psampsonee/elephant/hardware/LTSpice/buck-converter/tests/_archive/Sept 2026 Buck Converter Verification/notes/Curves/Energizer L92 - Internal Resistance Profile - X 0-1600 mAh - Y 0-0.8 Ohms.png.traj.ods

 | Pixels | Units
X | 272 | 400
Y | 174 | 0.2
Origin | 23
 | 704
Point | X-Pix | Y-Pix | mAh Used | Ohms
A | 23 | 424 | 0 | 0.11
 | 29 | 460 | 10 | 0.09
 | 50 | 484 | 43 | 0.08
 | 92 | 501 | 111 | 0.08
 | 150 | 511 | 204 | 0.07
 | 223 | 517 | 321 | 0.07
 | 297 | 521 | 440 | 0.07
 | 352 | 522 | 529 | 0.07
 | 570 | 537 | 879 | 0.06
 | 720 | 530 | 1120 | 0.07
 | 786 | 521 | 1226 | 0.07
 | 805 | 516 | 1256 | 0.07
 | 818 | 511 | 1277 | 0.07
 | 830 | 504 | 1296 | 0.08
 | 839 | 496 | 1311 | 0.08
 | 846 | 485 | 1322 | 0.08
 | 853 | 470 | 1333 | 0.09
 | 861 | 440 | 1346 | 0.10
 | 870 | 371 | 1361 | 0.13
 | 881 | 203 | 1378 | 0.19
 | 893 | 20 | 1398 | 0.26
