psampsonee/elephant/experiments/audio-test/LTSpice/dumb amplifier.asc

C1: cap; 10µ
C2: cap; {COUT}
C3: cap; 100n
D1: diode
D2: diode
Q1: npn
Q2: pnp
R1: res; 10k
R2: res; 10k
R3: res; 100
R4: res; {RBIAS}
R5: res; {RBIAS}
R6: res; {RLOAD}
R7: res; 4.7
R8: res; 4.7
Rf: res; 470k
Rin: res; 100k
U1: AD8542
V1: voltage; SINE({SIGOFF} {SIGAMP} {SIGF} 0); AC {SIGAMP} 0; Rser=10
V2: voltage; {VPOW}
Named nets: 0, VPow, VSig, VRef, VOut, Vout_OP, VB_Q1, VE_Q1, VB_Q2
.param VPOW=5
.param SIGMAXDC=3.3
.param SIGAMP=0.1
.param SIGOFF=SIGMAXDC/2
.param SIGF=50
 
.param RBIAS=1k
.param COUT=470u
.param RLOAD=7.3
.tran 0 1s 0
