psampsonee/elephant/hardware/LTSpice/buck-converter/Baseline/buck-test.asc

B1: bi; I={LOAD_I(V(V_BUCK_OUT),time)}
BATT1: L92; MAH_INIT={L92_MAH_INIT} L_SER=20n
BATT2: L92; MAH_INIT={L92_MAH_INIT} L_SER=20n
BATT3: L92; MAH_INIT={L92_MAH_INIT} L_SER=20n
BATT4: L92; MAH_INIT={L92_MAH_INIT} L_SER=20n
C1: cap; {C_1U}; V={C_1U_VOLTAGE_RATING} Rser={ESR_C_1U}
C2: cap; {C_TRSS}
C3: cap; {C_1U}; V={C_1U_VOLTAGE_RATING} Rser={ESR_C_1U}
C4: cap; {C_1U}; V={C_1U_VOLTAGE_RATING} Rser={ESR_C_1U}
C5: cap; {C_1U}; V={C_1U_VOLTAGE_RATING} Rser={ESR_C_1U}
C6: cap; {C_VIN_DISTAL}
C7: cap; {C_OUT}; IC={V_COUT_INIT}
C8: cap; {C_BIAS}
L1: ind; {L_SW}; Ipk={L_SW_I_SAT} Rser={DCR_L_SW_WORST}
R1: res; {R_BIAS_1}
R2: res; {R_BIAS_2}
R3: res; {R_RT}
U1: LT8640
V2: voltage; PWL(0 0 1u 0 2u 1)
Named nets: 0, MAIN_BAT+, BUCK_EN, V_BUCK_OUT
.tran 0 8m 6m 20n
.include buck-test.inc
.include "/home/paul/Desktop/Elephant LTSpice Folder/lib/sub/custom/L92/L92.mod"
(Note 1)
