psampsonee/elephant/hardware/LTSpice/power-or/Baseline/power-or-test.asc

C8: cap; {C_VBACKUP}
L1: ind; {L_BUCK}; Rser=1m
L6: ind; {L_COIN}; Rser=1m
R2: res; {R_ST_PRIORITY}
R3: res; {R_ST_SECONDARY}
V1: voltage; {V_BUCK}; Rser={R_BUCK}
V6: voltage; {V_COIN}; Rser={R_COIN}
X1: LM66100
X2: LM66100
Named nets: 0, COIN_BAT+, V_BUCK_OUT, V_BACKUP, V_BACKUP_STATUS
.include power-or-test.inc
.tran 0 10m 0 20n
