psampsonee/elephant/hardware/LTSpice/power-or/Baseline/tilt-sw-test.asc

B1: bi; I=I_SW(time)
C1: cap; {C_CHARGE}
D1: schottky; BAT54
D2: schottky; BAT54
D3: diode; 1N4148
D4: diode; 1N4148
M1: nmos; BSS138P
R1: res; {R_CHARGE}
R2: res; {R_DISCH}
R3: res; {R_GPIO_LEAKAGE}
Named nets: V_SW, 0, V_EN, V_RC, V_DD_STM32
.tran 0 30m 0 20n
.include tilt-sw-test.inc
.include tilt-sw-max-voltages.meas
.include "/home/paul/Desktop/Elephant LTSpice Folder/lib/sub/vendor/NXP BSS138P.sub"
