psampsonee/elephant/hardware/LTSpice/tilt-switch-wake/Tests/BSS138 Threshold Voltage/nfet-test.asc

M1: nmos; BSS138P
R1: res; {R_LEAK}
R2: res; {R_PULLUP}
V1: voltage; PWL(0 0 1u 0 1m 3)
V2: voltage; {V_SRC}
Named nets: 0, V_SWEEP, V_SENSE, VDD
.include nfet-test.inc
.include "/home/paul/Desktop/Elephant LTSpice Folder/lib/sub/vendor/NXP BSS138P.sub"
.tran 0 1m 0 20n
