psampsonee/elephant/firmware/Core/Inc/sys_preproc.h

//Preprocessor fallback values

#ifndef RTC_DATETIME
#define RTC_DATETIME

#define RTC_YEAR 1
#define RTC_MONTH 1
#define RTC_DAY 1

#define RTC_HOUR 1
#define RTC_MINUTE 1
#define RTC_SECOND 1

#define RTC_WEEKDAY 1

#define RTC_MAGIC 0

#endif /* RTC_DATETIME */
