psampsonee/elephant/experiments/gpio-assert-test/gpio-assert-test.ioc

Mcu.UserName=STM32F401CCUx
PA13.Signal=SYS_JTMS-SWDIO
PA14.Signal=SYS_JTCK-SWCLK
PA4.Signal=GPIO_Output
PA5.Signal=SPI1_SCK
PA6.Signal=SPI1_MISO
PA7.Signal=SPI1_MOSI
PB10.Signal=I2S2_CK
PB12.Signal=I2S2_WS
PB15.Signal=I2S2_SD
PB3.Signal=GPIO_Output
PB6.Signal=S_TIM4_CH1
PC13-ANTI_TAMP.Signal=GPIO_Output
