psampsonee/elephant/experiments/audio-test/Audio/Src/PCM_sample_source.cpp

#include "storage_device.h"
#include "sample_source.h"
#include "PCM_sample_source.h"

/* Initialization
 * Prepares SampleSource upon system startup
 * Tasks:
 * Check that startup invariants are valid:
 * Sample workspace size >= storage device sector size
 * Initialize storage
 * Call reset()
 */
bool PCMSampleSource::init() {
    reset();

    if (storage_.getSectorSize() > MAX_SECTOR_SIZE_BYTES) {
        return false;
    }

    if (!storage_.init()) {
        return false;
    }

    return true;
}

/* Start
 * Tasks:
 * Set all sample parameters to first reading state
 */
bool PCMSampleSource::start(size_t clipStartSector) {
    workspaceIndex_ = 0;
    workspaceSectorOffset_ = clipStartSector;

    fillWorkspace();
    if(!workspaceValid_) {
        return false;
    }

    ready_ = true;
    return true;
}

/* Reset
 * Tasks:
 * Set all parameters to initial states.
 */
void PCMSampleSource::reset() {
    workspaceIndex_ = 0;
    workspaceSectorOffset_ = 0;
    std::memset(workspace_, 0, sizeof(workspace_));
}

/* getSample
 * Tasks:
 * Check runtime invariants and prevent them from being violated:
 *  Can't get a sample when the source is not ready.
 *
 * destination aways gets written to starting at index 0.
 */

    // workspaceIndex_ is a persistent variable starting at 0.
    // upon start(clipStartSector), workspace_ is filled with the first sector.
    // samplesPerSector = storage_.getSectorSize() / sizeof(int16_t)
    // samplesRemaining = sampleCount
    // samplesWritten = 0
    // While samplesRemaining > 0:
    //  samplesLeftInWorkspace = samplesPerSector - workspaceIndex_
    //  if ( samplesLeftInWorkspace == 0 ):
    //      workspaceSectorOffset_ += 1
    //      workspaceIndex_ = 0
    //      write the contents of the sector into the workspace as int16_t
    //      continue
    //  samplesToCopy = min(samplesRemaining, samplesLeftInWorkspace)
    //  For every i from 0 to samplesToCopy-1:
    //   destination[i+samplesWritten] = workspace_[workspaceIndex_]
    //   workspaceIndex_ += 1
    //  samplesWritten += samplesToCopy
    //  samplesRemaining -= samplesToCopy

bool PCMSampleSource::getSamples(int16_t* destination, std::size_t sampleCount) {

    if(!ready_) {
        return false;
    }

    std::size_t samplesPerSector = storage_.getSectorSize() / sizeof(int16_t);
    std::size_t samplesRemaining = sampleCount;
    std::size_t samplesWritten = 0;

    while ( samplesRemaining > 0 ) {
        std::size_t samplesLeftInWorkspace = samplesPerSector - workspaceIndex_;
        if(samplesLeftInWorkspace == 0) {
            workspaceValid_ = false;
        }

        if (!workspaceValid_) {
            fillWorkspace();
            if(!workspaceValid_) {
                return true;
            }

            continue;
        }

        std::size_t samplesToCopy =
            ( samplesLeftInWorkspace > samplesRemaining ?
            samplesRemaining : samplesLeftInWorkspace );

        for (std::size_t i = 0; i < samplesToCopy; i++) {
            destination[samplesWritten+i] = workspace_[workspaceIndex_];
            workspaceIndex_ += 1;
        }

        samplesWritten += samplesToCopy;
        samplesRemaining -= samplesToCopy;
    }

    return true;
}

std::size_t PCMSampleSource::getReadPositionSamples() const {
    if(!ready_) {
        return 0;
    }

    const std::size_t samplesPerSector =
        storage_.getSectorSize() / sizeof(int16_t);

    return workspaceSectorOffset_ * samplesPerSector + workspaceIndex_;
}

bool PCMSampleSource::fillWorkspace() {
        auto nextSector = workspaceSectorOffset_ + 1;
        auto readResult=storage_.read(workspaceSectorOffset_,
                                      reinterpret_cast<uint8_t*>(workspace_));

        if (readResult == StorageDevice::ReadResult::Error) {
            return false;
        }

        if (readResult == StorageDevice::ReadResult::NotReady) {
            workspaceValid_ = false;
            return true; // no fatal error, but leave buffer needing refill
        }

        workspaceValid_ = true;
        workspaceIndex_ = 0;
        workspaceSectorOffset_ = nextSector;
        return true;
}
